TjadenWright/VR-Glove/Hardware/3D Print/STLs/Parts/Battery Pack/Battery Upgrade Lid/batteryUpgradeLid v6.stl

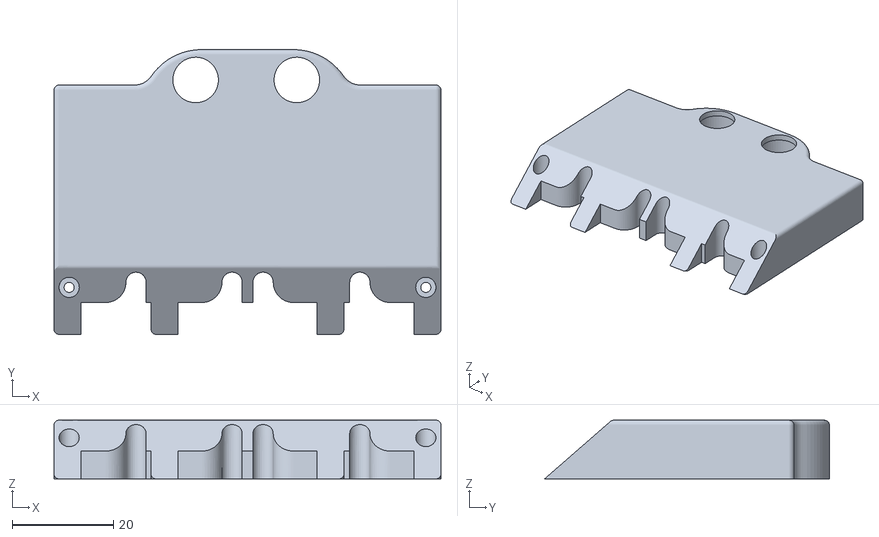
[picture p19: CAD file, 2024-10-23]
Hardware/3D Print/STLs/Parts/Battery Pack/Battery Upgrade Lid/batteryUpgradeLid v6.stl
76.5 x 56.3 x 11.6
