TjadenWright/VR-Glove/Hardware/3D Print/STLs/Parts/Battery Pack/Case Lid Top For Battery/caseLidTopForBattery v3.stl

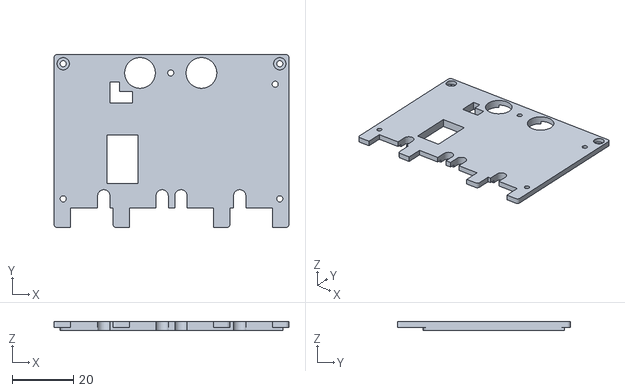
[picture p20: CAD file, 2024-10-23]
Hardware/3D Print/STLs/Parts/Battery Pack/Case Lid Top For Battery/caseLidTopForBattery v3.stl
76.5 x 56.3 x 3.00
