TjadenWright/VR-Glove/Hardware/3D Print/STLs/Parts/Joystick And Buttons/Joystick Body/joystickBody v8.stl

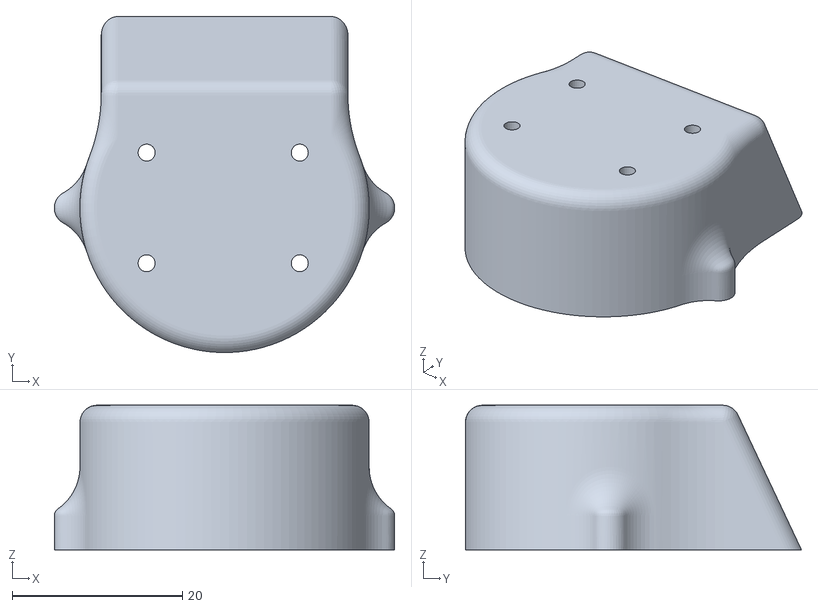
[picture p21: CAD file, 2024-10-23]
Hardware/3D Print/STLs/Parts/Joystick And Buttons/Joystick Body/joystickBody v8.stl
40.0 x 39.5 x 17.0
