TjadenWright/VR-Glove/Hardware/3D Print/STLs/Parts/Joystick And Buttons/Joystick Finger Mount/joystickFingerMount v6.stl

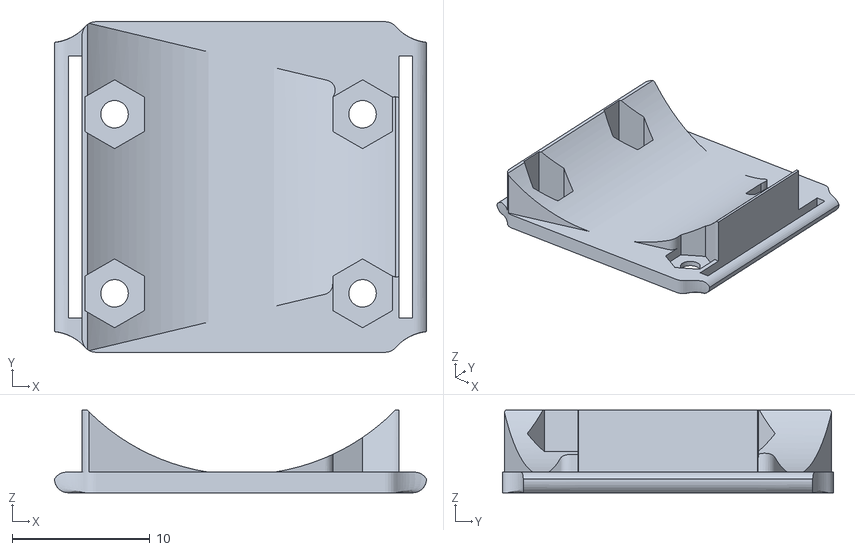
[picture p22: CAD file, 2024-10-23]
Hardware/3D Print/STLs/Parts/Joystick And Buttons/Joystick Finger Mount/joystickFingerMount v6.stl
27.0 x 24.0 x 6.00
