TjadenWright/VR-Glove/Hardware/3D Print/STLs/Parts/Joystick And Buttons/Joystick Lid/joystickLid v12.stl

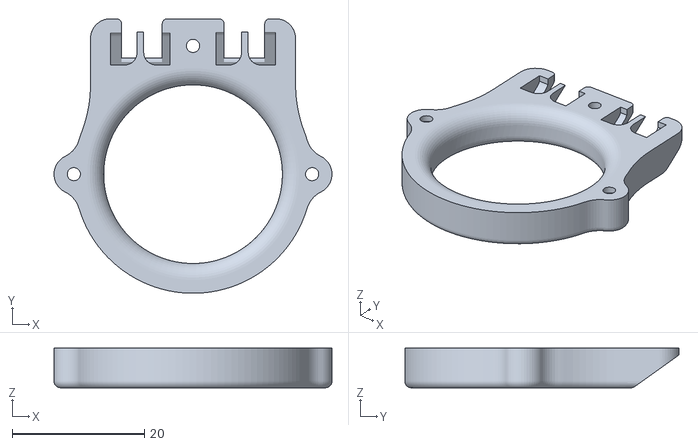
[picture p23: CAD file, 2024-10-23]
Hardware/3D Print/STLs/Parts/Joystick And Buttons/Joystick Lid/joystickLid v12.stl
42.0 x 41.5 x 6.00
