TjadenWright/VR-Glove/Hardware/3D Print/STLs/Parts/Joystick And Buttons/Joystick Mount/joystickMount v2.stl

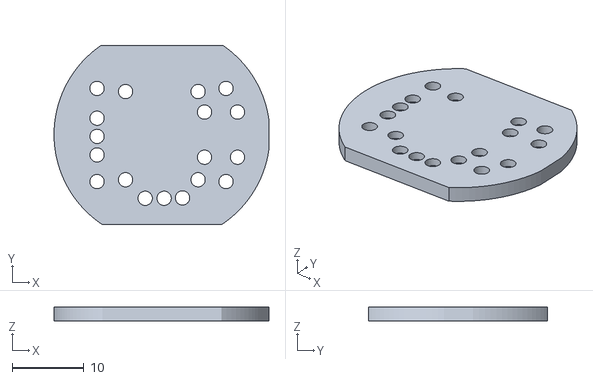
[picture p24: CAD file, 2024-10-23]
Hardware/3D Print/STLs/Parts/Joystick And Buttons/Joystick Mount/joystickMount v2.stl
30.0 x 25.0 x 2.00
