TjadenWright/VR-Glove/Hardware/3D Print/STLs/Parts/Base Parts/Bar Magnet/barMagnet v13.stl

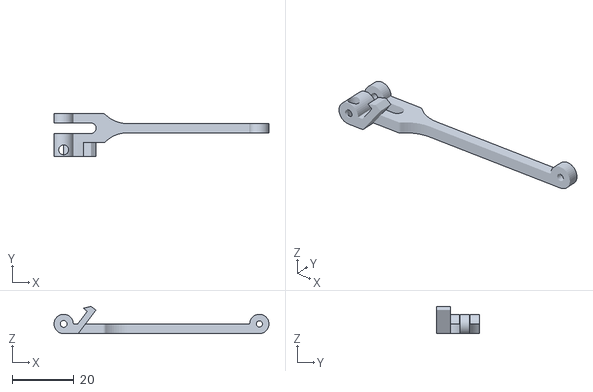
[picture p25: CAD file, 2024-10-23]
Hardware/3D Print/STLs/Parts/Base Parts/Bar Magnet/barMagnet v13.stl
69.4 x 13.8 x 8.79
