TjadenWright/VR-Glove/Hardware/3D Print/STLs/Parts/Base Parts/Bar/bar v8.stl

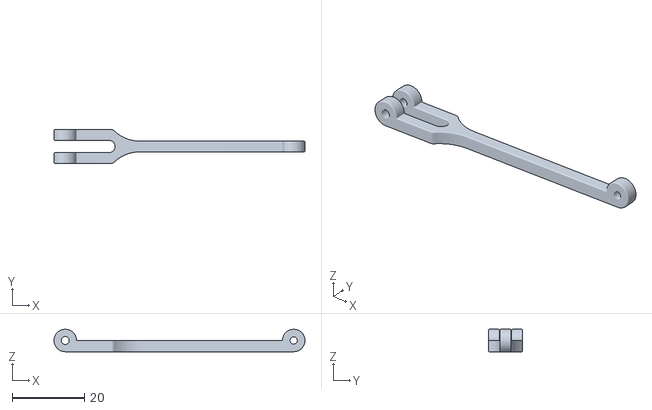
[picture p26: CAD file, 2024-10-23]
Hardware/3D Print/STLs/Parts/Base Parts/Bar/bar v8.stl
69.4 x 9.40 x 6.25
