TjadenWright/VR-Glove/Software/VR Glove - LucidVR/lucidgloves-firmware/input.ino

#include <esp_adc_cal.h>
#include <Preferences.h>
//#include <EEPROM.h>

Preferences prefs;

// Requires RunningMedian library by Rob Tillaart
#if (ENABLE_MEDIAN_FILTER || ((INTERFILTER_MODE != INTERFILTER_NONE) && (FLEXION_MIXING != MIXING_NONE)) || (INTERFILTER_MODE == INTERFILTER_LIMITS))
  #include <RunningMedian.h>
#endif

#if ENABLE_MEDIAN_FILTER
  RunningMedian rmSamples[2* NUM_FINGERS] = {
      RunningMedian(MEDIAN_SAMPLES),
      RunningMedian(MEDIAN_SAMPLES),
      RunningMedian(MEDIAN_SAMPLES),
      RunningMedian(MEDIAN_SAMPLES),
      RunningMedian(MEDIAN_SAMPLES),
      RunningMedian(MEDIAN_SAMPLES),
      RunningMedian(MEDIAN_SAMPLES),
      RunningMedian(MEDIAN_SAMPLES),
      RunningMedian(MEDIAN_SAMPLES),
      RunningMedian(MEDIAN_SAMPLES)
  };

  RunningMedian rmSamplesJoystick[2] = {
      RunningMedian(MEDIAN_SAMPLES),
      RunningMedian(MEDIAN_SAMPLES),
  };
#endif

#if ((INTERFILTER_MODE != INTERFILTER_NONE) && (FLEXION_MIXING == MIXING_SINCOS))
  RunningMedian sinSamples[NUM_FINGERS] = {
      RunningMedian(INTERFILTER_SAMPLES),
      RunningMedian(INTERFILTER_SAMPLES),
      RunningMedian(INTERFILTER_SAMPLES),
      RunningMedian(INTERFILTER_SAMPLES),
      RunningMedian(INTERFILTER_SAMPLES)
  };

    RunningMedian cosSamples[NUM_FINGERS] = {
      RunningMedian(INTERFILTER_SAMPLES),
      RunningMedian(INTERFILTER_SAMPLES),
      RunningMedian(INTERFILTER_SAMPLES),
      RunningMedian(INTERFILTER_SAMPLES),
      RunningMedian(INTERFILTER_SAMPLES)
  };
#endif

#if ((INTERFILTER_MODE == INTERFILTER_LIMITS) || (INTERFILTER_MODE == INTERFILTER_ALL))
  RunningMedian calibSamples[2* NUM_FINGERS] = {
      RunningMedian(INTERFILTER_SAMPLES),
      RunningMedian(INTERFILTER_SAMPLES),
      RunningMedian(INTERFILTER_SAMPLES),
      RunningMedian(INTERFILTER_SAMPLES),
      RunningMedian(INTERFILTER_SAMPLES),
      RunningMedian(INTERFILTER_SAMPLES),
      RunningMedian(INTERFILTER_SAMPLES),
      RunningMedian(INTERFILTER_SAMPLES),
      RunningMedian(INTERFILTER_SAMPLES),
      RunningMedian(INTERFILTER_SAMPLES)
  };
#endif


#define DEFAULT_VREF 1100
esp_adc_cal_characteristics_t *adc_chars;

byte selectPins[] = {PINS_MUX_SELECT};

int maxFingers[2* NUM_FINGERS] = {0,0,0,0,0,0,0,0,0,0}; // {1943, 2129, 2128, 2062, 2206, 2077, 2252, 2276, 2235, 2236};
int minFingers[2* NUM_FINGERS] = {ANALOG_MAX, ANALOG_MAX, ANALOG_MAX, ANALOG_MAX, ANALOG_MAX, ANALOG_MAX, ANALOG_MAX, ANALOG_MAX, ANALOG_MAX, ANALOG_MAX}; // {1839, 1927, 1792, 1789, 1759, 1721, 2191, 2252, 2218, 2206};
int maxTravel[2*NUM_FINGERS] = {ANALOG_MAX, ANALOG_MAX, ANALOG_MAX, ANALOG_MAX, ANALOG_MAX, ANALOG_MAX, ANALOG_MAX, ANALOG_MAX, ANALOG_MAX, ANALOG_MAX};
#if FLEXION_MIXING == MIXING_SINCOS
  int sinMin[NUM_FINGERS] = {ANALOG_MAX, ANALOG_MAX, ANALOG_MAX, ANALOG_MAX, ANALOG_MAX};
  int sinMax[NUM_FINGERS] = {0,0,0,0,0};

  int cosMin[NUM_FINGERS] = {ANALOG_MAX, ANALOG_MAX, ANALOG_MAX, ANALOG_MAX, ANALOG_MAX};
  int cosMax[NUM_FINGERS] = {0,0,0,0,0};

  bool atanPositive[NUM_FINGERS] = {true, true, true, true, true};


  int totalOffset1[NUM_FINGERS] = {0,0,0,0,0};
#endif


bool savedInter = false;
bool savedTravel = false;

void setupInputs(){
  prefs.begin("LucidGloves");
  //EPROM.begin(0x78 + 1);
  Serial.begin(115200); //DON'T FORGET TO REMOVE THISSSSS
  Serial.println("Setting up input!");
  if (isSavedLimits()){
    Serial.println("Is saved limits!");
    savedTravel = true;
    loadTravel();
  }
  if (isSavedIntermediate() && FLEXION_MIXING != MIXING_NONE){ // Check to make sure we're even using mixing. If someone had the wrong mixing type set before, this will cause an issue!
    Serial.println("IsSavedIntermediate!");
    savedInter = true;
    loadIntermediate();
  }

  pinMode(PIN_JOY_BTN, INPUT_PULLUP);
  pinMode(PIN_A_BTN, INPUT_PULLUP);
  pinMode(PIN_B_BTN, INPUT_PULLUP);

  #if !GRAB_GESTURE
  pinMode(PIN_GRAB_BTN, INPUT_PULLUP);
  #endif

  #if !PINCH_GESTURE
  pinMode(PIN_PNCH_BTN, INPUT_PULLUP);
  #endif

  #if USING_CALIB_PIN
  pinMode(PIN_CALIB, INPUT_PULLUP);
  #endif

  #if USING_TWO_CALIB_PINS
  pinMode(PIN_CALIB_FLEX, INPUT_PULLUP);
  pinMode(PIN_CALIB_SPLAY, INPUT_PULLUP);
  #endif

  #if USING_MULTIPLEXER
  byte selectPins[] = {PINS_MUX_SELECT};
  //pinMode(MUX_INPUT, INPUT);
  for (int i = 0; i < sizeof(selectPins); i++){
    pinMode(selectPins[i], OUTPUT);
  }
  #endif
}

int analogPinRead(int pin){
  #if USING_MULTIPLEXER
  if (ISMUX(pin)){
    return readMux(UNMUX(pin));
  }
  else{
    return analogRead(pin);
  }
  #else
   return analogRead(pin);
  #endif
}

#if USING_MULTIPLEXER
int readMux(byte pin){
  int numSelectPins = sizeof(selectPins) / sizeof(selectPins[0]);

  for (int i = numSelectPins - 1; i > -1; i--){
    digitalWrite(selectPins[i], (pin & (1 << i)) ? HIGH : LOW);
  }

  delayMicroseconds(MULTIPLEXER_DELAY);
  return analogRead(MUX_INPUT);
}
#endif

int targetSinMin, targetSinMax, targetSinCurrent, targetCosMin, targetCosMax, targetCosCurrent, targetFlexionMin, targetFlexionMax, targetFlexionCurrent, targetMaxTravel, targetProcessed;
void getFingerPositions(bool calibrating, bool reset, bool flexion, bool splay){
  #if FLEXION_MIXING == MIXING_NONE //no mixing, just linear
  int rawFingersFlexion[NUM_FINGERS] = {NO_THUMB?0:analogPinRead(PIN_THUMB), analogPinRead(PIN_INDEX), analogPinRead(PIN_MIDDLE), analogPinRead(PIN_RING), analogPinRead(PIN_PINKY)};
  
  #elif FLEXION_MIXING == MIXING_SINCOS
  int rawFingersFlexion[NUM_FINGERS] = {NO_THUMB?0:sinCosMix(PIN_THUMB, PIN_THUMB_SECOND, 0 ), 
                                  sinCosMix(PIN_INDEX, PIN_INDEX_SECOND, 1 ), 
                                  sinCosMix(PIN_MIDDLE,PIN_MIDDLE_SECOND,2 ), 
                                  sinCosMix(PIN_RING,  PIN_RING_SECOND,  3 ), 
                                  sinCosMix(PIN_PINKY, PIN_PINKY_SECOND, 4 )};

  #endif

  int rawFingers[2 * NUM_FINGERS];
  int rawFingersCalib[2 * NUM_FINGERS];

  #if USING_SPLAY
    int rawFingersSplay[NUM_FINGERS] = {NO_THUMB?0:analogPinRead(PIN_THUMB_SPLAY), 
                              analogPinRead(PIN_INDEX_SPLAY), 
                              analogPinRead(PIN_MIDDLE_SPLAY), 
                              analogPinRead(PIN_RING_SPLAY), 
                              analogPinRead(PIN_PINKY_SPLAY)};
  #else
    int rawFingersSplay[NUM_FINGERS] = {0,0,0,0,0};
  #endif
    //memcpy(rawFingers, rawFingersFlexion, 5); //memcpy doesn't seem to work here
    //memcpy(&rawFingers[5], rawFingersSplay, 5); 

  for (int i = 0; i < NUM_FINGERS; i++){
    rawFingers[i] = rawFingersFlexion[i];
    rawFingers[i+NUM_FINGERS] = rawFingersSplay[i];
  }
  
  
  //flip pot values if needed
  #if FLIP_FLEXION
  for (int i = 0; i < NUM_FINGERS; i++){
    rawFingers[i] = ANALOG_MAX - rawFingers[i];
  }
  #endif
  
  #if FLIP_SPLAY
  for (int i = NUM_FINGERS; i < 2 * NUM_FINGERS; i++){
    rawFingers[i] = ANALOG_MAX - rawFingers[i];
  }
  #endif
  
  #if ENABLE_MEDIAN_FILTER
  for (int i = 0; i < 2 * NUM_FINGERS; i++){
    #if CLAMP_SENSORS_DISCARD
      if(rawFingers[i] < CLAMP_MAX && rawFingers[i] > CLAMP_MIN){
        rmSamples[i].add( rawFingers[i] );
      }
    #else
      rmSamples[i].add( rawFingers[i] );
    #endif
    rawFingers[i] = rmSamples[i].getMedian();
  }
  #endif

  //reset max and mins as needed
  if (reset){
    if (flexion){
      for (int i = 0; i <NUM_FINGERS; i++){
        #if FLEXION_MIXING == MIXING_SINCOS
        if (i < NUM_FINGERS)
          totalOffset1[i] = 0;
        #endif
        maxFingers[i] = 0;
        minFingers[i] = ANALOG_MAX;
      }
    }

    if (splay){
      for (int i = NUM_FINGERS; i <2*NUM_FINGERS; i++){
        maxFingers[i] = 0;
        minFingers[i] = ANALOG_MAX;
      }
    }
  }
  
  //if during the calibration sequence, make sure to update max and mins
  if (calibrating){
    // new array just for calibration
    for (int i = 0; i < 2 * NUM_FINGERS; i++){
      rawFingersCalib[i] = rawFingers[i];
    }
    // do we need to filter?
    #if ((INTERFILTER_MODE == INTERFILTER_LIMITS) || (INTERFILTER_MODE == INTERFILTER_ALL))
      for (int i = 0; i < 2 * NUM_FINGERS; i++){
        #if CLAMP_SENSORS_DISCARD
          if(rawFingersCalib[i] < CLAMP_MAX && rawFingersCalib[i] > CLAMP_MIN){
            calibSamples[i].add( rawFingersCalib[i] );
          }
        #else
        calibSamples[i].add( rawFingersCalib[i] );
        #endif
        rawFingersCalib[i] = calibSamples[i].getMedian();
      }
    #endif
    if(flexion){
      for (int i = 0; i < NUM_FINGERS; i++){
        if (rawFingersCalib[i] > maxFingers[i])
          #if CLAMP_SENSORS
            maxFingers[i] = ( rawFingersCalib[i] <= CLAMP_MAX )? rawFingersCalib[i] : CLAMP_MAX;
          #elif CLAMP_SENSORS_DISCARD
            if(rawFingersCalib[i] < CLAMP_MAX && rawFingersCalib[i] > CLAMP_MIN){
              maxFingers[i] = ( rawFingersCalib[i] <= CLAMP_MAX )? rawFingersCalib[i] : CLAMP_MAX;
            }
          #else
            maxFingers[i] = rawFingersCalib[i];
            if (savedTravel && (maxFingers[i] - minFingers[i] > maxTravel[i]))
                minFingers[i] = maxFingers[i] - maxTravel[i];
          #endif
        if (rawFingersCalib[i] < minFingers[i])
          #if CLAMP_SENSORS
            minFingers[i] = ( rawFingersCalib[i] >= CLAMP_MIN )? rawFingersCalib[i] : CLAMP_MIN;
          #elif CLAMP_SENSORS_DISCARD
            if(rawFingers[i] < CLAMP_MAX && rawFingersCalib[i] > CLAMP_MIN){
              minFingers[i] = ( rawFingersCalib[i] >= CLAMP_MIN )? rawFingersCalib[i] : CLAMP_MIN;
            }
          #else
            minFingers[i] = rawFingersCalib[i];
            if (savedTravel && (maxFingers[i] - minFingers[i] > maxTravel[i]))
                maxFingers[i] = minFingers[i] + maxTravel[i];
          #endif
      }
    }

    if(splay){
      for (int i = NUM_FINGERS; i < 2*NUM_FINGERS; i++){
        if (rawFingersCalib[i] > maxFingers[i])
          #if CLAMP_SENSORS
            maxFingers[i] = ( rawFingersCalib[i] <= CLAMP_MAX )? rawFingersCalib[i] : CLAMP_MAX;
          #elif CLAMP_SENSORS_DISCARD
            if(rawFingersCalib[i] < CLAMP_MAX && rawFingers[i] > CLAMP_MIN){
              maxFingers[i] = ( rawFingersCalib[i] <= CLAMP_MAX )? rawFingersCalib[i] : CLAMP_MAX;
            }
          #else
            maxFingers[i] = rawFingersCalib[i];
            if (savedTravel && (maxFingers[i] - minFingers[i] > maxTravel[i]))
                minFingers[i] = maxFingers[i] - maxTravel[i];
          #endif
        if (rawFingersCalib[i] < minFingers[i])
          #if CLAMP_SENSORS
            minFingers[i] = ( rawFingersCalib[i] >= CLAMP_MIN )? rawFingersCalib[i] : CLAMP_MIN;
          #elif CLAMP_SENSORS_DISCARD
            if(rawFingersCalib[i] < CLAMP_MAX && rawFingersCalib[i] > CLAMP_MIN){
              minFingers[i] = ( rawFingersCalib[i] >= CLAMP_MIN )? rawFingersCalib[i] : CLAMP_MIN;
            }
          #else
            minFingers[i] = rawFingersCalib[i];
            if (savedTravel && (maxFingers[i] - minFingers[i] > maxTravel[i]))
                maxFingers[i] = minFingers[i] + maxTravel[i];
          #endif
      }
    }
  }
  
  for (int i = 0; i < 2*NUM_FINGERS; i++){
    if (minFingers[i] != maxFingers[i]){
      #if !CLAMP_SENSORS_DISCARD
      fingerPos[i] = map( rawFingers[i], minFingers[i], maxFingers[i], 0, ANALOG_MAX );
      #else
      // for clamp discard, you can not set finger pose if not right since it's passed by reference.
      if(rawFingers[i] < CLAMP_MAX && rawFingers[i] > CLAMP_MIN){
        fingerPos[i] = map( rawFingers[i], minFingers[i], maxFingers[i], 0, ANALOG_MAX );
      }
      #endif
      #if CLAMP_ANALOG_MAP
        if (fingerPos[i] < 0)
          fingerPos[i] = 0;
        if (fingerPos[i] > ANALOG_MAX)
          fingerPos[i] = ANALOG_MAX;
      #endif
    }
    else {
      fingerPos[i] = ANALOG_MAX / 2;
    }
    
  }
}

int analogReadDeadzone(int pin){
  int raw = analogPinRead(pin);

  #if ENABLE_MEDIAN_FILTER
    if(pin == PIN_JOY_X){
      rmSamplesJoystick[0].add(raw);
      raw = rmSamplesJoystick[0].getMedian();
    }
    else{
      rmSamplesJoystick[1].add(raw);
      raw = rmSamplesJoystick[1].getMedian();
    }
  #endif

  if (abs(ANALOG_MAX/2 - raw) < JOYSTICK_DEADZONE * ANALOG_MAX / 100)
    return ANALOG_MAX/2;
  else{
    #if JOYSTICK_MAPPING
      // map the pins
      if(pin == PIN_JOY_X){ // x
        raw = map(raw, JOYSTICK_X_MIN, JOYSTICK_X_MAX, 0, ANALOG_MAX );
      }
      else{ // y
        raw = map(raw, JOYSTICK_Y_MIN, JOYSTICK_Y_MAX, 0, ANALOG_MAX );
      }
      
      // check if outside bounds, if so clamp
      if(raw > ANALOG_MAX || raw < 0){ // keep within bounds
        if(raw < 0)
          raw = 0;
        else
          raw = ANALOG_MAX;
      }
    #endif
    
    return raw;
  }
}

int getJoyX(){
  #if JOYSTICK_BLANK
  return ANALOG_MAX/2;
  #elif JOY_FLIP_X
    return ANALOG_MAX - analogReadDeadzone(PIN_JOY_X);
  #else
    return analogReadDeadzone(PIN_JOY_X);
  #endif
}

int getJoyY(){
  #if JOYSTICK_BLANK
  return ANALOG_MAX/2;
  #elif JOY_FLIP_Y
    return ANALOG_MAX - analogReadDeadzone(PIN_JOY_Y);
  #else
    return analogReadDeadzone(PIN_JOY_Y);
  #endif
}

bool getButton(byte pin){
  return digitalRead(pin) != HIGH;
}

#if FLEXION_MIXING == MIXING_SINCOS
//mixing
int sinCosMix(int sinPin, int cosPin, int i){

  int sinRaw = analogPinRead(sinPin);
  int cosRaw = analogPinRead(cosPin);

  #if INTERFILTER_MODE != INTERFILTER_NONE
    sinSamples[i].add(sinRaw);
    cosSamples[i].add(cosRaw);
    int sinCalib = sinSamples[i].getMedian();
    int cosCalib = cosSamples[i].getMedian();
    #if INTERFILTER_MODE == INTERFILTER_ALL
      sinRaw = sinCalib;
      cosRaw = cosCalib;
    #endif
  #else
    int sinCalib = sinRaw;
    int cosCalib = cosRaw;
  #endif 

  if (!savedInter){
    //scaling
    sinMin[i] = min(sinCalib, sinMin[i]);
    sinMax[i] = max(sinCalib, sinMax[i]);

    cosMin[i] = min(cosCalib, cosMin[i]);
    cosMax[i] = max(cosCalib, cosMax[i]);
  }

  if (i==target){
    targetSinMin = sinMin[i];
    targetSinMax = sinMax[i];
    targetSinCurrent = sinRaw;
    targetCosMin = cosMin[i];
    targetCosMax = cosMax[i];
    targetCosCurrent = cosRaw;
  }

  int sinScaled = map(sinRaw, sinMin[i], sinMax[i], -ANALOG_MAX, ANALOG_MAX);
  int cosScaled = map(cosRaw, cosMin[i], cosMax[i], -ANALOG_MAX, ANALOG_MAX);


  //trigonometry stuffs
  double angleRaw = atan2(sinScaled, cosScaled);

  //counting rotations
  if (((angleRaw > 0) != atanPositive[i]) && sinScaled > cosScaled){
    totalOffset1[i] += atanPositive[i]?1:-1;
  }
  atanPositive[i] = angleRaw > 0;
  double totalAngle = angleRaw + 2*PI * totalOffset1[i];
  

  return (int)(totalAngle * ANALOG_MAX);
  
}
#endif

void saveTravel()
{
  prefs.putBytes("maxTravel", (byte*)(&maxTravel), sizeof(maxTravel));

  /*byte flags = EEPROM.read(0x00);
  flags |= 0x01;  // Set bit 0
  EEPROM.write(0x00, flags); // Save clamping saved limits flag

  int addr = 0x01;  // Start address for flexion and splay values

  for (int i = 0; i < 2*NUM_FINGERS; i++) {
    int diff = maxFingers[i] - minFingers[i]; // Calculate the difference
    EEPROM.put(addr, diff); // Store the difference into the EEPROM at the current address
    addr += sizeof(int); // Increment the address by 4 because we're storing int values
  }
  
  EEPROM.commit(); // Ensure changes are written to EEPROM

  loadTravel();*/
}

void saveIntermediate()
{
  // prefs.putBytes("sinMax", (byte*)(&sinMax), sizeof(sinMax));
  // prefs.putBytes("sinMin", (byte*)(&sinMin), sizeof(sinMin));
  // prefs.putBytes("cosMax", (byte*)(&cosMax), sizeof(cosMax));
  // prefs.putBytes("cosMin", (byte*)(&cosMin), sizeof(cosMin));

  /*byte flags = EEPROM.read(0x00);
  flags |= 0x02;  // Set bit 1
  EEPROM.write(0x00, flags); // Save intermediate values saved flag

  int address = 0x29; // Start address for sin and cos values

  for(int i = 0; i < NUM_FINGERS; i++)
  {
    EEPROM.put(address, sinMax[i]);
    address += sizeof(int);
    EEPROM.put(address, sinMin[i]);
    address += sizeof(int);
    EEPROM.put(address, cosMax[i]);
    address += sizeof(int);
    EEPROM.put(address, cosMin[i]);
    address += sizeof(int);
  }
  
  EEPROM.commit(); // Ensure changes are written to EEPROM*/
}

void clearFlags()
{
  prefs.clear();

  /*EEPROM.write(0x00, 0x00); // Clear the flags
  EEPROM.commit(); // Ensure the changes are written to EEPROM*/
}

bool isSavedLimits()
{
  return (prefs.getBytesLength("maxTravel") != 0);

  /*byte flags = EEPROM.read(0x00);
  return flags & 0x01;  // Check bit 0 */
}

bool isSavedIntermediate()
{
  return (prefs.getBytesLength("sinMax") > 0 && prefs.getBytesLength("sinMin") > 0 && prefs.getBytesLength("cosMax") > 0 && prefs.getBytesLength("cosMin") > 0);

  /*byte flags = EEPROM.read(0x00);
  return flags & 0x02;  // Check bit 1*/
}

void loadTravel()
{
  if(prefs.getBytesLength("maxTravel") == 0);
    return; // If clamping saved limits is not stored, do nothing
  prefs.getBytes("maxTravel", &maxTravel, sizeof(maxTravel));

  /*byte flags = EEPROM.read(0x00);
  if (!(flags & 0x01)) return; // If clamping saved limits flag is not set, do nothing

  int addr = 0x01;  // Start address for flexion and splay values

  for (int i = 0; i < 2*NUM_FINGERS; i++) {
    EEPROM.get(addr, maxTravel[i]); // Load the max travel value from the EEPROM at the current address
    addr += sizeof(int); // Increment the address by 4 because we're storing int values
  }*/
}

void loadIntermediate()
{
  if(prefs.getBytesLength("maxTravel") == 0 | prefs.getBytesLength("sinMin") == 0 | prefs.getBytesLength("cosMax") == 0 | prefs.getBytesLength("cosMin") == 0);
    return; // If clamping saved limits is not stored, do nothing  
  // prefs.getBytes("sinMax", &sinMax, sizeof(sinMax));
  // prefs.getBytes("sinMin", &sinMin, sizeof(sinMin));
  // prefs.getBytes("cosMax", &cosMax, sizeof(cosMax));
  // prefs.getBytes("cosMin", &cosMin, sizeof(cosMin));

  /*byte flags = EEPROM.read(0x00);
  if (!(flags & 0x02)) return; // If intermediate values saved flag is not set, do nothing

  int address = 0x29; // Start address for sin and cos values

  for(int i = 0; i < NUM_FINGERS; i++)
  {
    EEPROM.get(address, sinMax[i]);
    address += sizeof(int);

    EEPROM.get(address, sinMin[i]);
    address += sizeof(int);

    EEPROM.get(address, cosMax[i]);
    address += sizeof(int);

    EEPROM.get(address, cosMin[i]);
    address += sizeof(int);
  }*/
}
